jaisor/SmartPoolThermometer/src/Device.h

#pragma once

#include <functional>
#include "Configuration.h"
#include "wifi/SensorProvider.h"

#ifdef TEMP_SENSOR_DS18B20
  #include <OneWire.h>
  #include <DS18B20.h>
#endif
#ifdef TEMP_SENSOR_BME280
  #include <Adafruit_Sensor.h>
  #include <Adafruit_BME280.h>
#endif
#ifdef TEMP_SENSOR_DHT
  #include <DHT.h>
  #include <DHT_U.h>
#endif
#ifdef TEMP_SENSOR_AHT
  #include <Adafruit_AHTX0.h>
#endif

#define STALE_READING_AGE_MS 10000 // 10 sec

class CDevice: public ISensorProvider {

public:
	CDevice();
  ~CDevice();
  void loop();

  virtual uint32_t getDeviceId();
  virtual unsigned long getUptime() { return millis() - tMillisUp; };
  virtual bool isSensorReady() { return sensorReady; };

#if defined(TEMP_SENSOR_DS18B20) || defined(TEMP_SENSOR_DHT) || defined(TEMP_SENSOR_AHT)
  virtual float getTemperature(bool *current);
#endif
#if defined(TEMP_SENSOR_BME280) || defined(TEMP_SENSOR_DHT) || defined(TEMP_SENSOR_AHT)
  virtual float getHumidity(bool *current);
#endif
#if defined(TEMP_SENSOR_BME280)
  virtual float getAltitude(bool *current);
#endif
#ifdef BATTERY_SENSOR
  virtual float getBatteryVoltage(bool *current);
#endif

private:
  unsigned long tMillisUp;

  unsigned long tMillisTemp;
  unsigned long tLastReading;
  bool sensorReady;
  
  float _temperature;
#ifdef TEMP_SENSOR_DS18B20
  OneWire *oneWire;
  DS18B20 *_ds18b20;
#endif
#ifdef TEMP_SENSOR_BME280
  float _humidity, _altitude;
  Adafruit_BME280 *_bme;
#endif
#ifdef TEMP_SENSOR_DHT
  float _humidity;
  DHT_Unified *_dht;
  unsigned long minDelayMs;
#endif
#ifdef TEMP_SENSOR_AHT
  float _humidity;
  Adafruit_AHTX0 *_aht;
  unsigned long minDelayMs;
#endif
};
